0xDBFB7/simple-LAFM/20171120012839_2_0.jpg

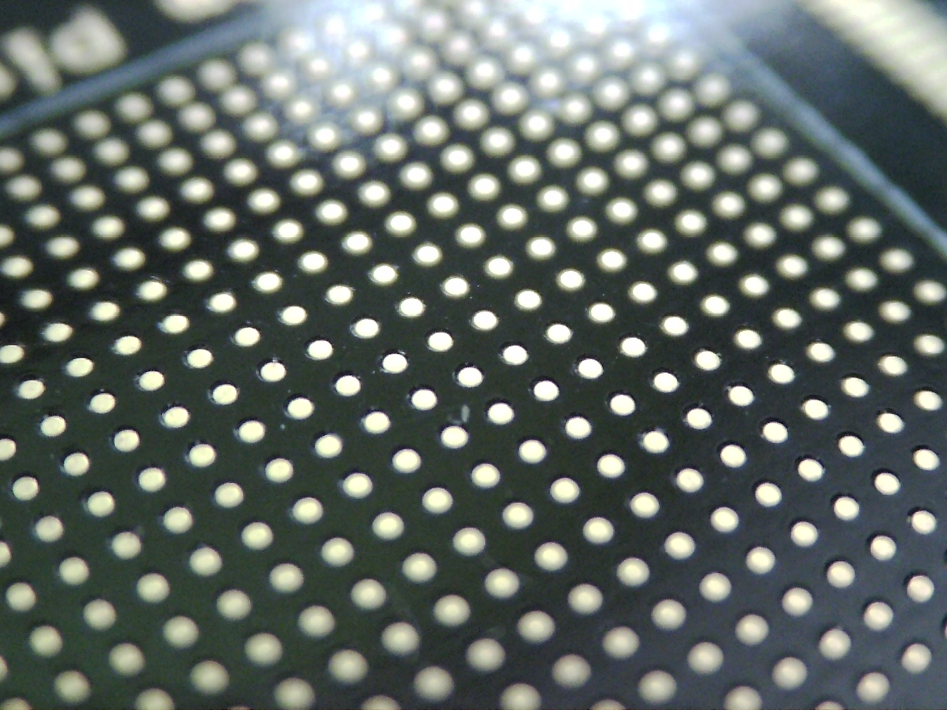
20171120012839_2_0.jpg
